StefansAI/TTL-6510-Computer/docs/assets/images/pcb_revA.jpg

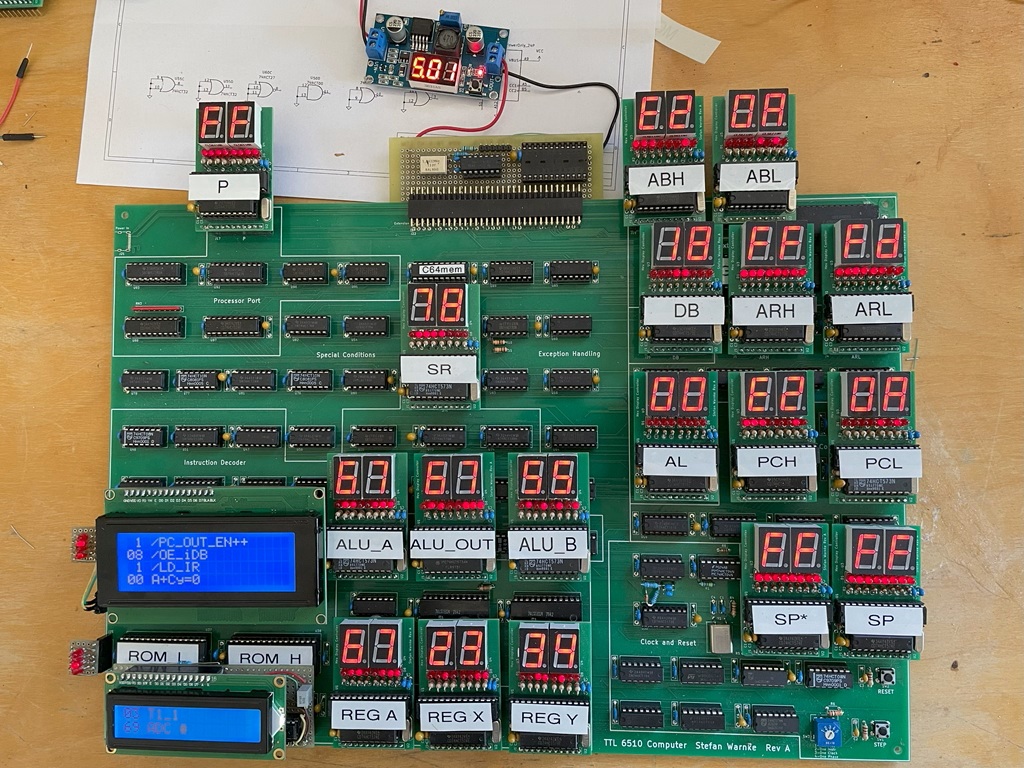
docs/assets/images/pcb_revA.jpg
