StefansAI/TTL-6510-Computer/docs/assets/images/pcb_revA_cropped.jpg

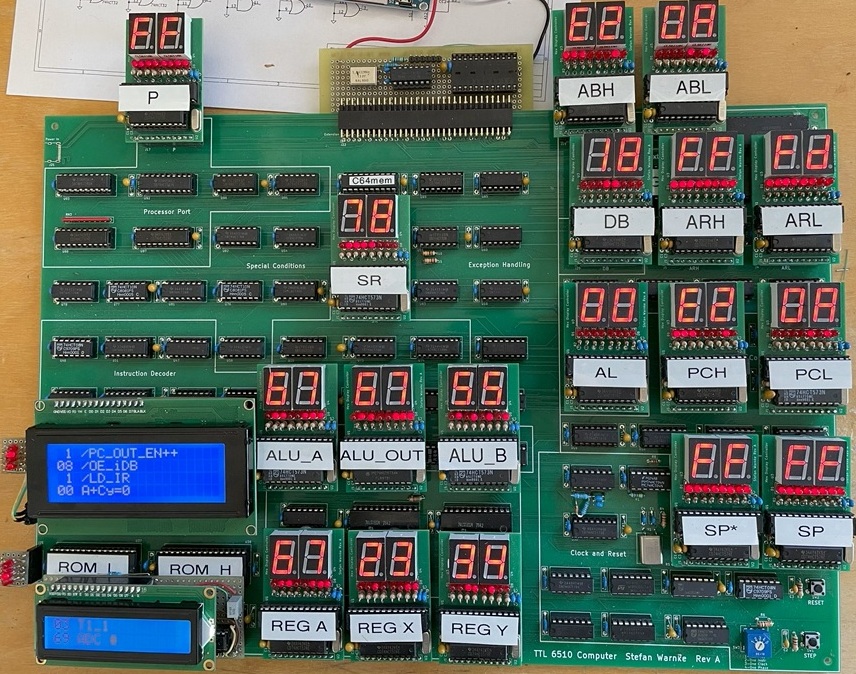
docs/assets/images/pcb_revA_cropped.jpg
